richardhawthorn/wifi-tft-1.44/images/1-DSC_0450.JPG

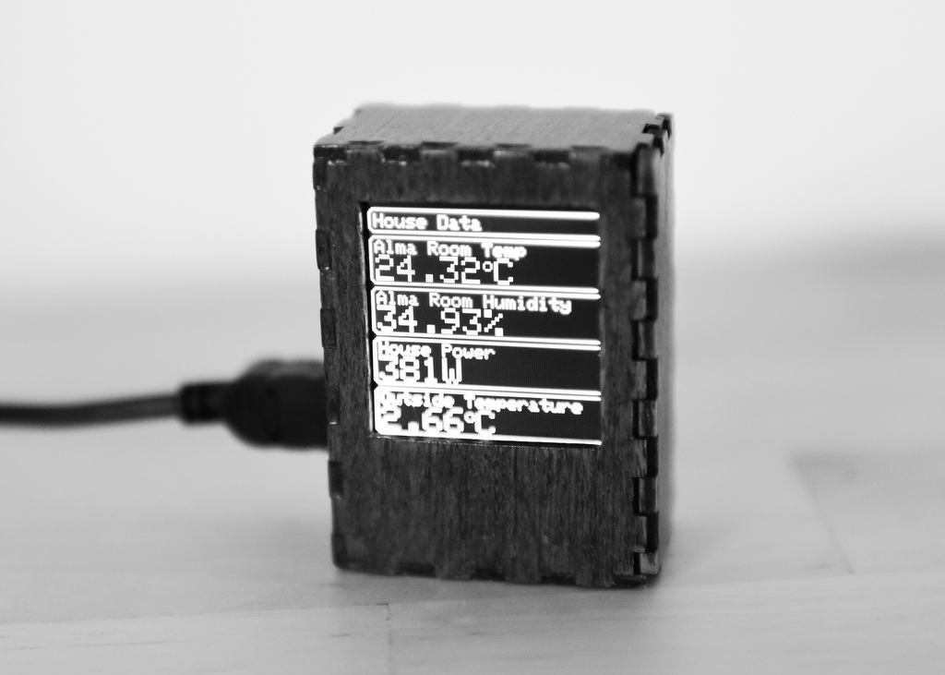
images/1-DSC_0450.JPG
