richardhawthorn/wifi-tft-1.44/images/pcb_back.png

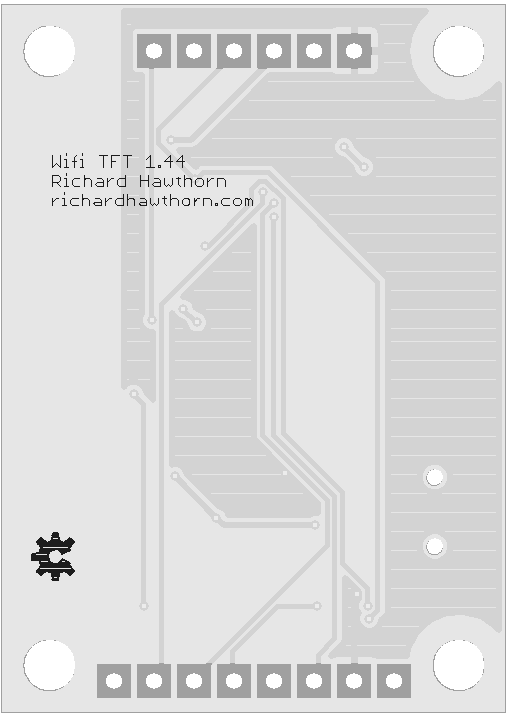
images/pcb_back.png
